amminadabz/Synharmonium/Sketches and Mockups/1.png

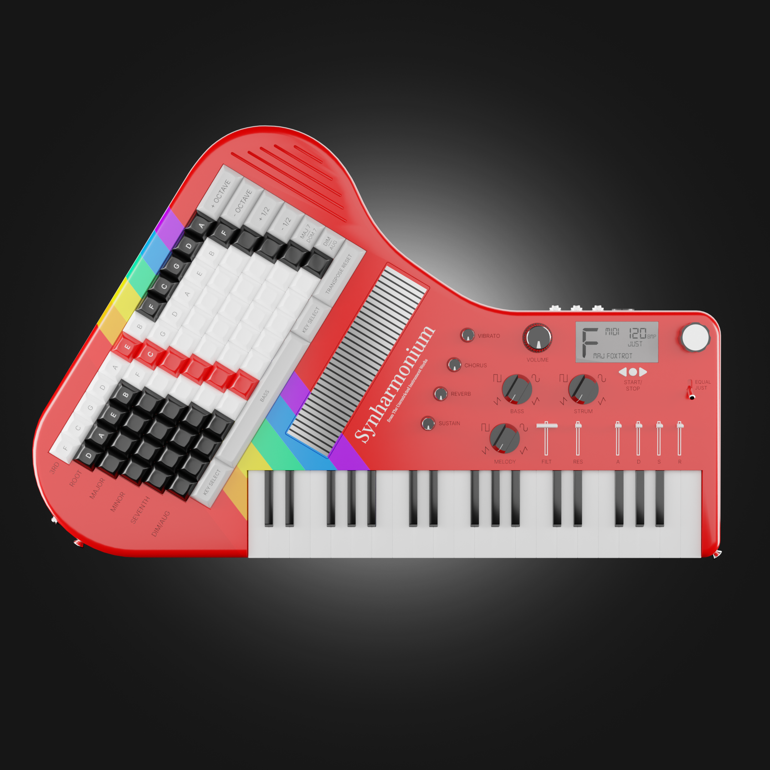
Sketches and Mockups/1.png
