amminadabz/Synharmonium/Sketches and Mockups/1_w.png

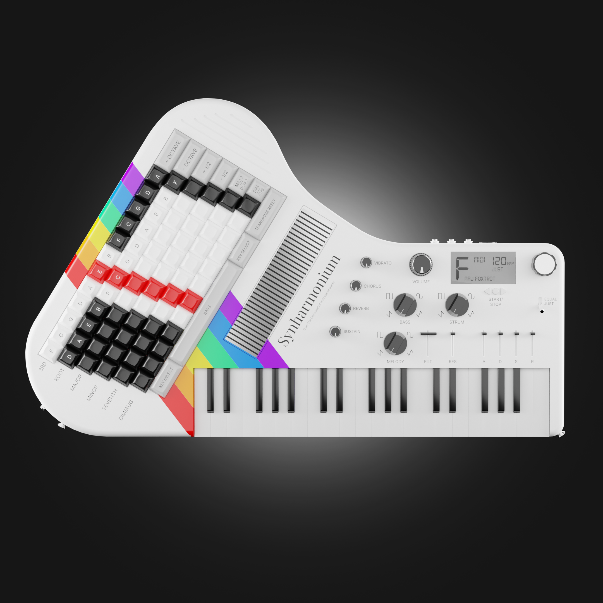
Sketches and Mockups/1_w.png
