amminadabz/Synharmonium/Sketches and Mockups/2.png

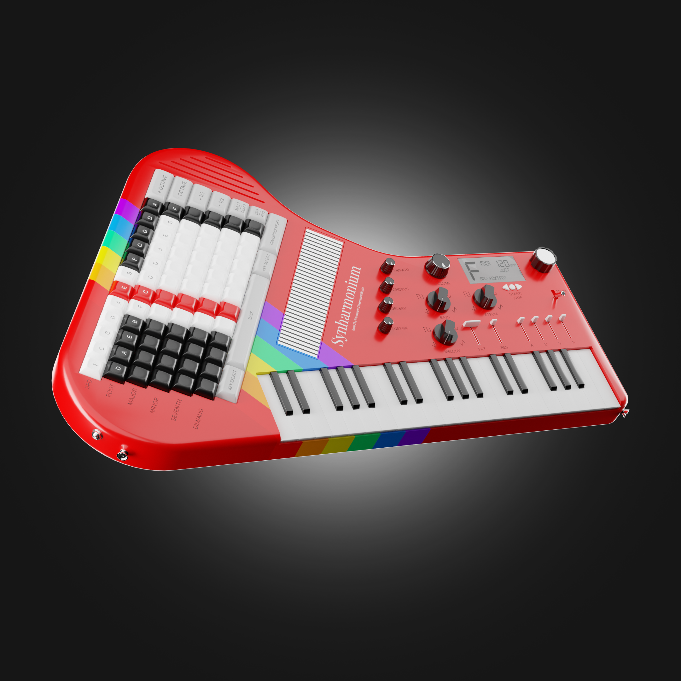
Sketches and Mockups/2.png
