amminadabz/Synharmonium/Sketches and Mockups/3.png

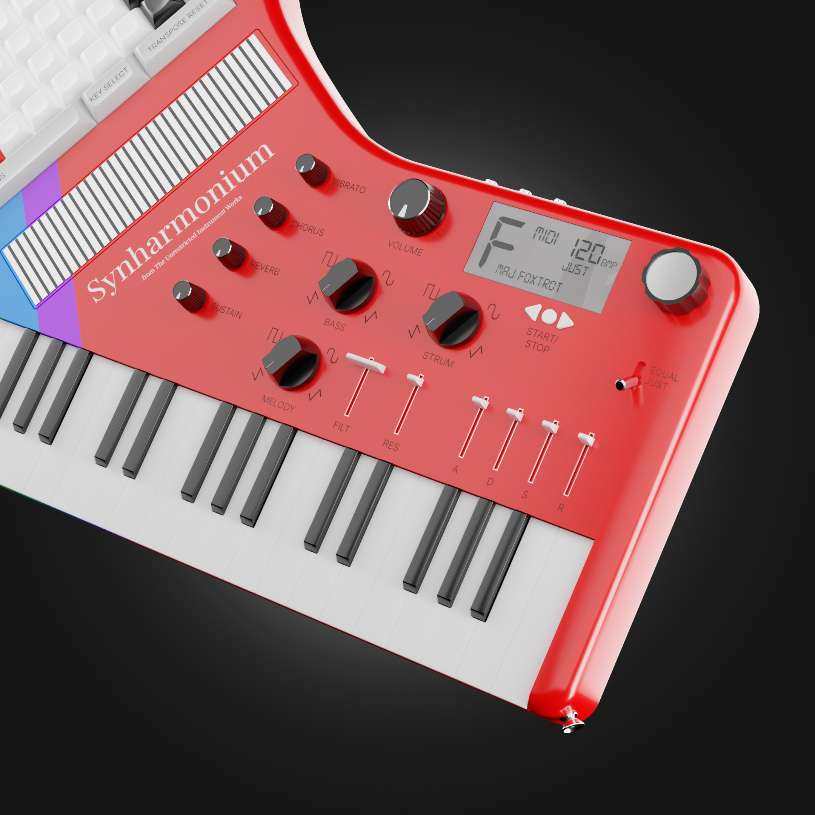
Sketches and Mockups/3.png
