amminadabz/Synharmonium/Sketches and Mockups/3_b.png

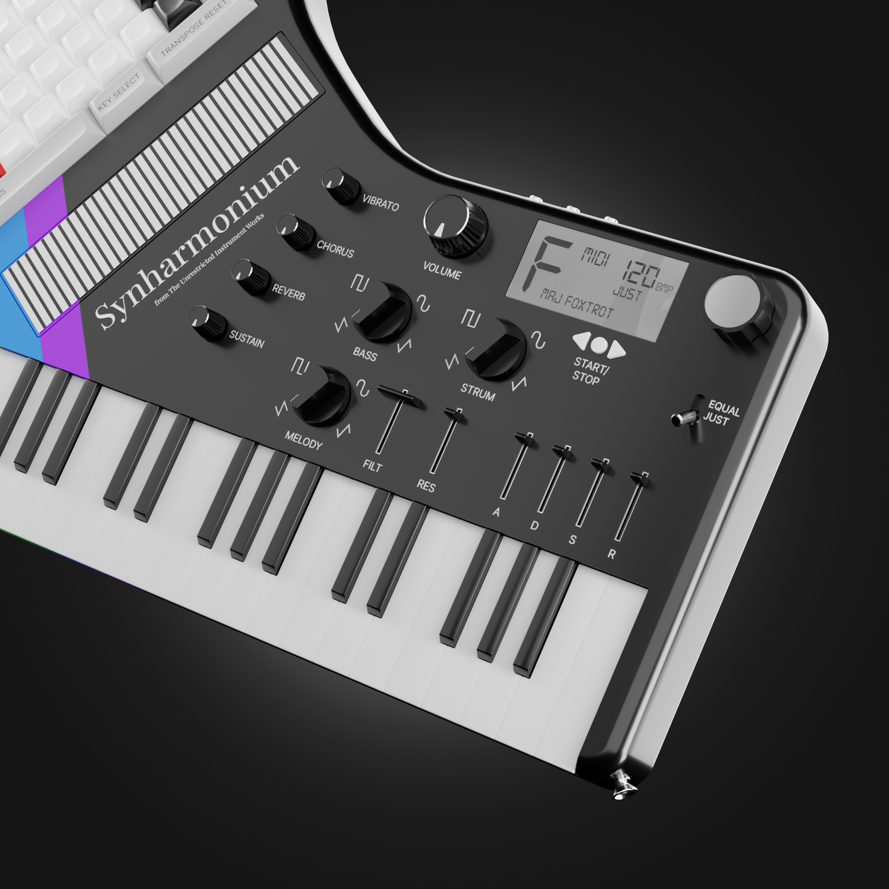
Sketches and Mockups/3_b.png
