amminadabz/Synharmonium/Sketches and Mockups/3_w.png

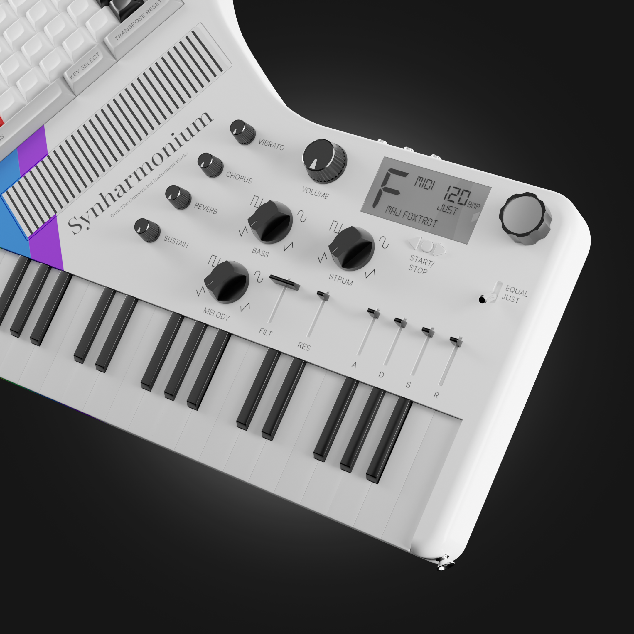
Sketches and Mockups/3_w.png
