amminadabz/Synharmonium/Sketches and Mockups/bass-keyboard-layout.png

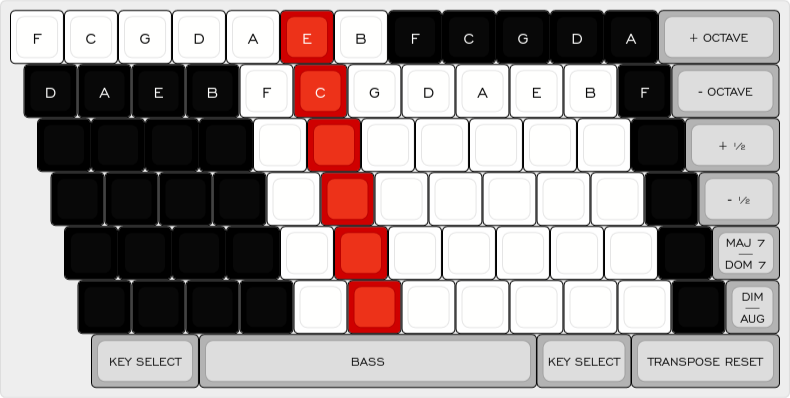
Sketches and Mockups/bass-keyboard-layout.png
