amminadabz/Synharmonium/Sketches and Mockups/bass_keyboard_pcb_render_back.png

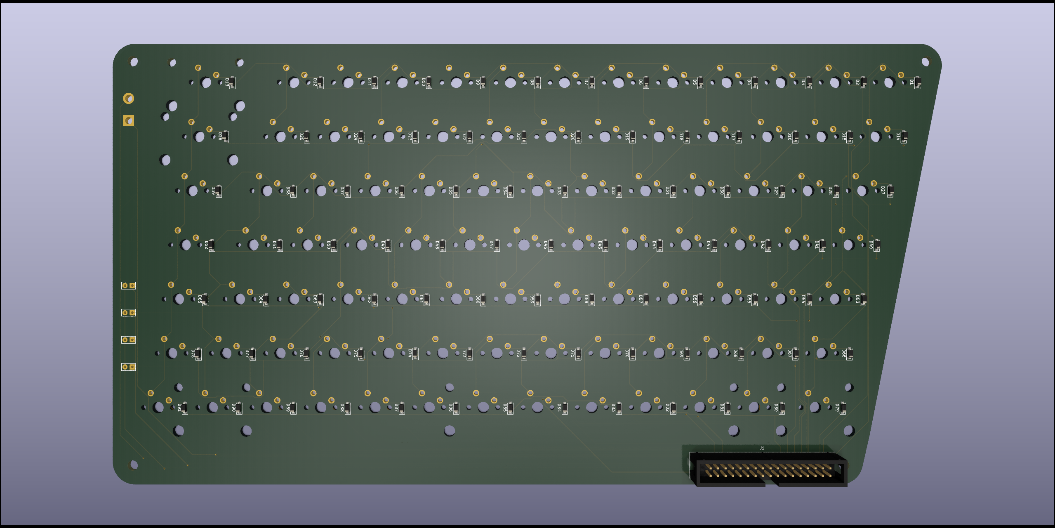
Sketches and Mockups/bass_keyboard_pcb_render_back.png
