amminadabz/Synharmonium/Sketches and Mockups/bass_keyboard_pcb_render_front.png

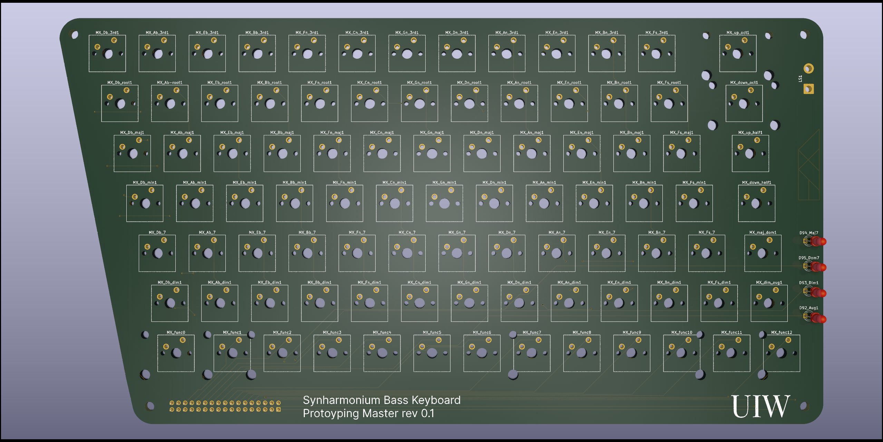
Sketches and Mockups/bass_keyboard_pcb_render_front.png
