amminadabz/Synharmonium/Sketches and Mockups/sketch-1-cleaner.jpeg

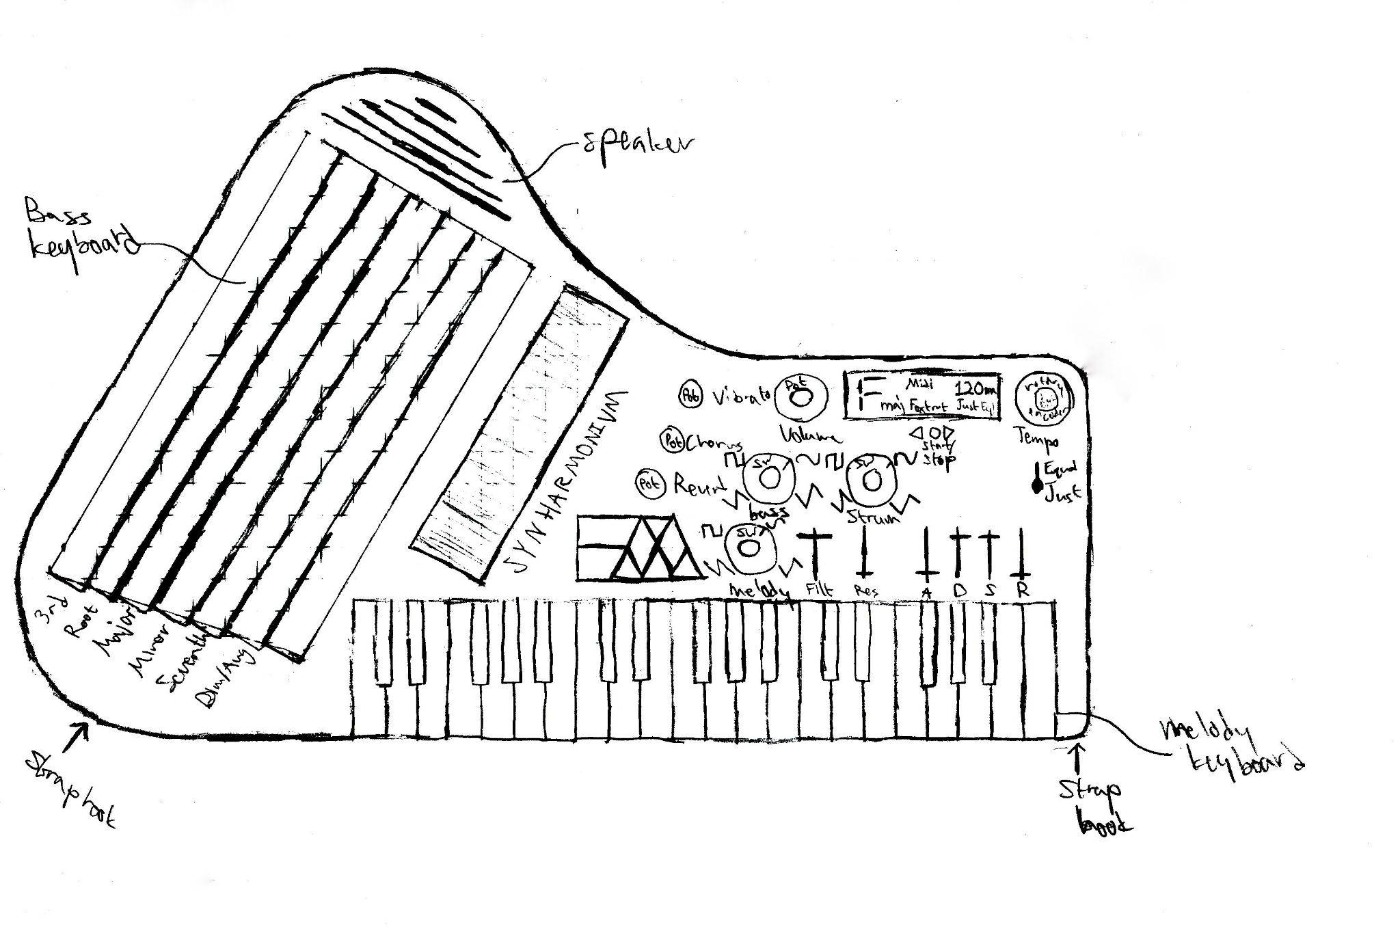
Sketches and Mockups/sketch-1-cleaner.jpeg
