amminadabz/Synharmonium/Hardware/bass_keyboard/Prototype Keycap Models/DSA/Light Gray/1x/1.50.3mf

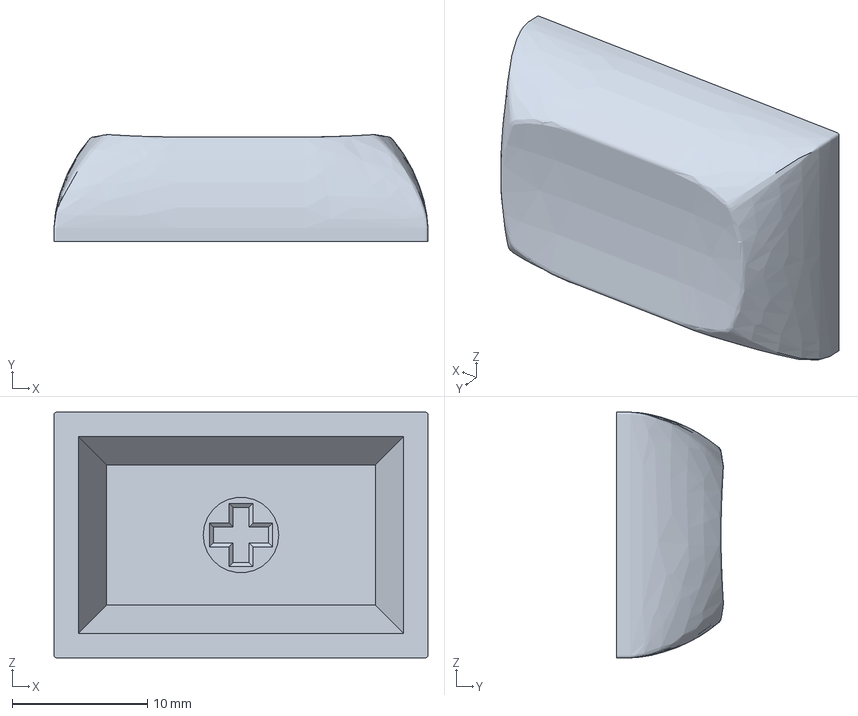
[picture p27: CAD file, 2023-05-22]
Hardware/bass_keyboard/Prototype Keycap Models/DSA/Light Gray/1x/1.50.3mf
27.7 x 7.91 x 18.2 mm
