amminadabz/Synharmonium/Hardware/bass_keyboard/Prototype Keycap Models/DSA/Light Gray/1x/6.25.3mf

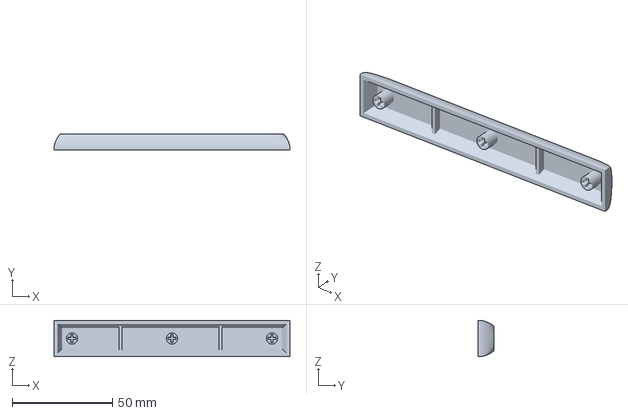
[picture p28: CAD file, 2023-05-22]
Hardware/bass_keyboard/Prototype Keycap Models/DSA/Light Gray/1x/6.25.3mf
118.0 x 8.00 x 18.2 mm
