amminadabz/Synharmonium/Hardware/bass_keyboard/Prototype Keycap Models/DSA/Light Gray/1x/2.75.3mf

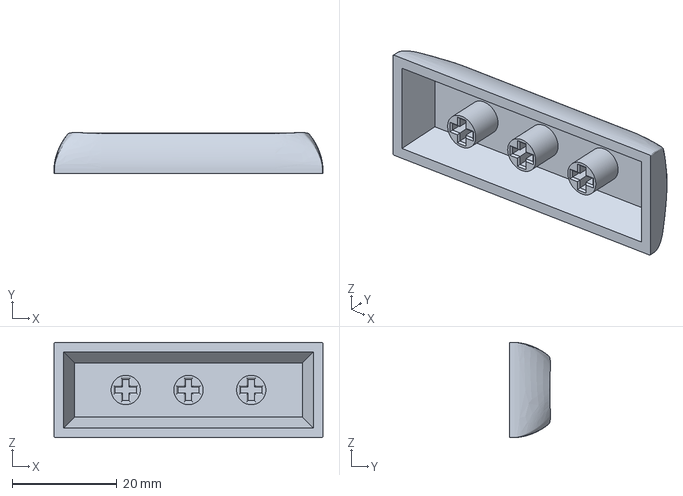
[picture p29: CAD file, 2023-05-22]
Hardware/bass_keyboard/Prototype Keycap Models/DSA/Light Gray/1x/2.75.3mf
51.5 x 7.91 x 18.2 mm
